Bunny350/FilaCab/STL/Filament rolling/roller-toolless_X2.stl

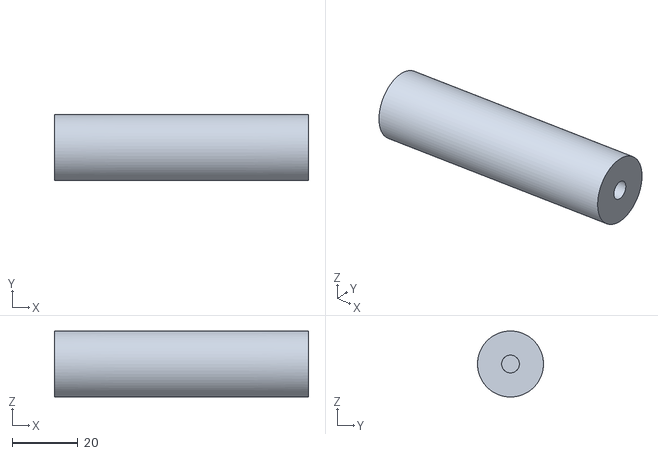
[picture p16: CAD file, 2026-09-27]
STL/Filament rolling/roller-toolless_X2.stl
77.0 x 20.0 x 20.0
